alxrxs/tsc/Images/pcb_iso.png

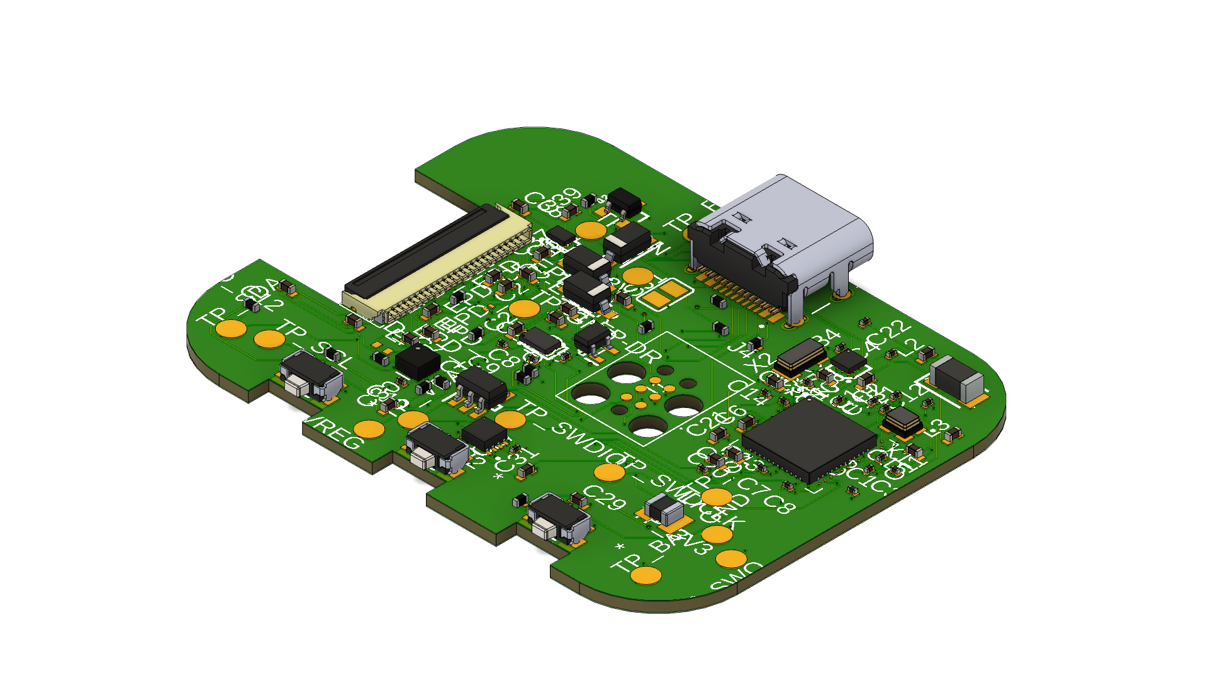
Images/pcb_iso.png
