alxrxs/tsc/Images/pcb_left.png

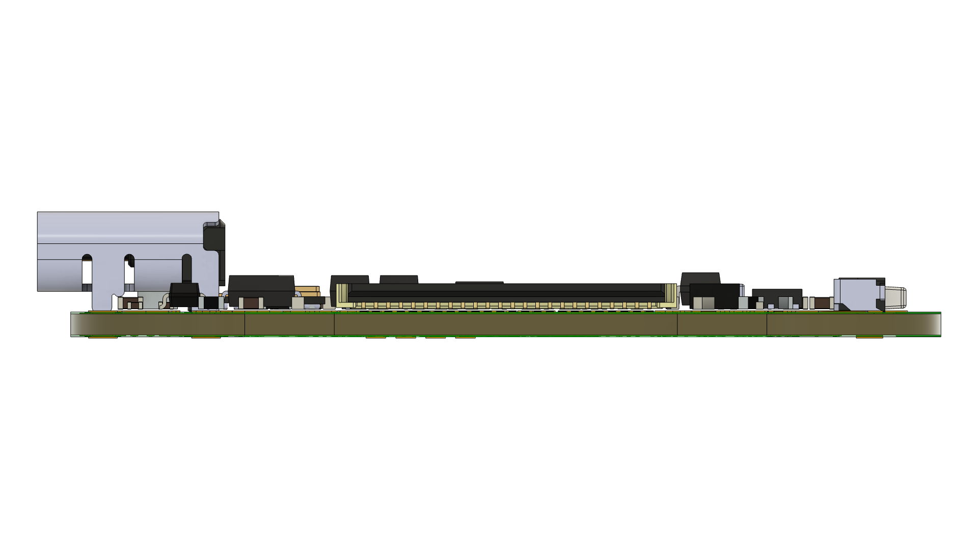
Images/pcb_left.png
