alxrxs/tsc/Images/render_front.png

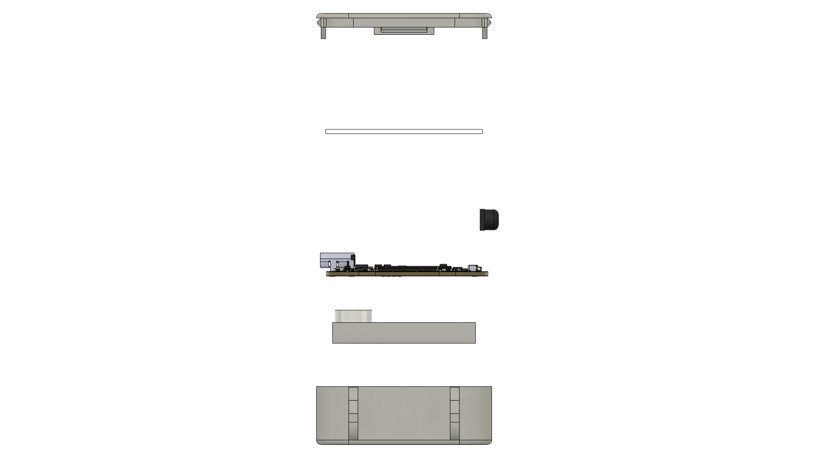
Images/render_front.png
